lemio/w-esp/w-esp-web-app/button-01.png

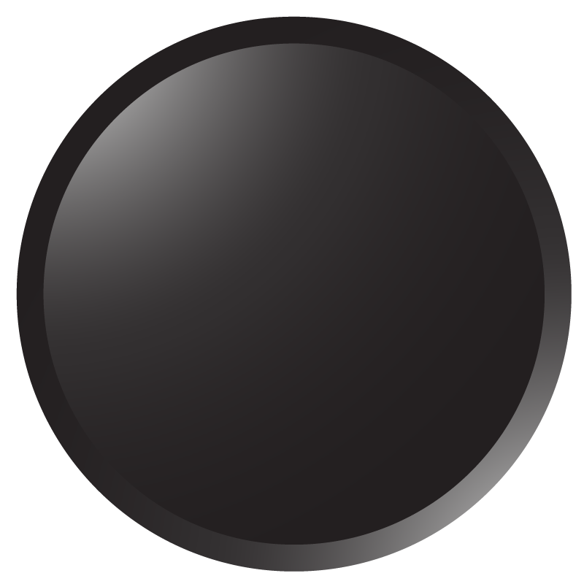
w-esp-web-app/button-01.png
