lemio/w-esp/w-esp-web-app/button-02.png

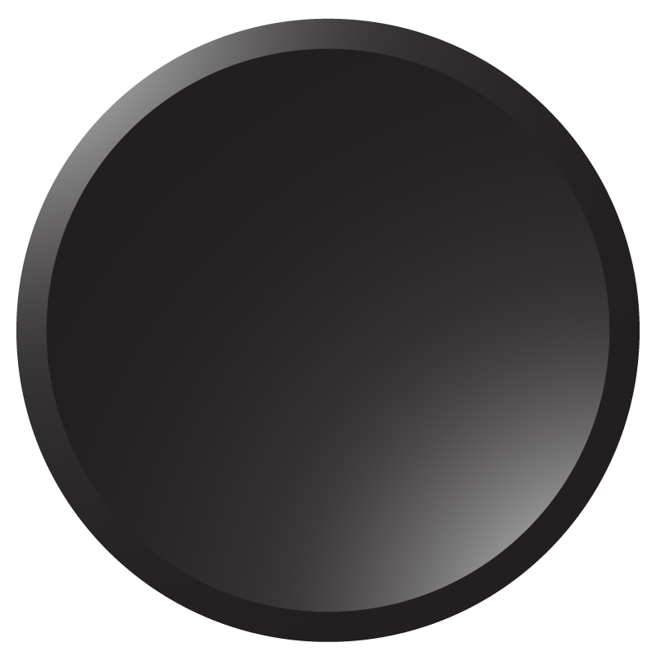
w-esp-web-app/button-02.png
